hxlnt/open_spectre/documentation/analoge side.PNG

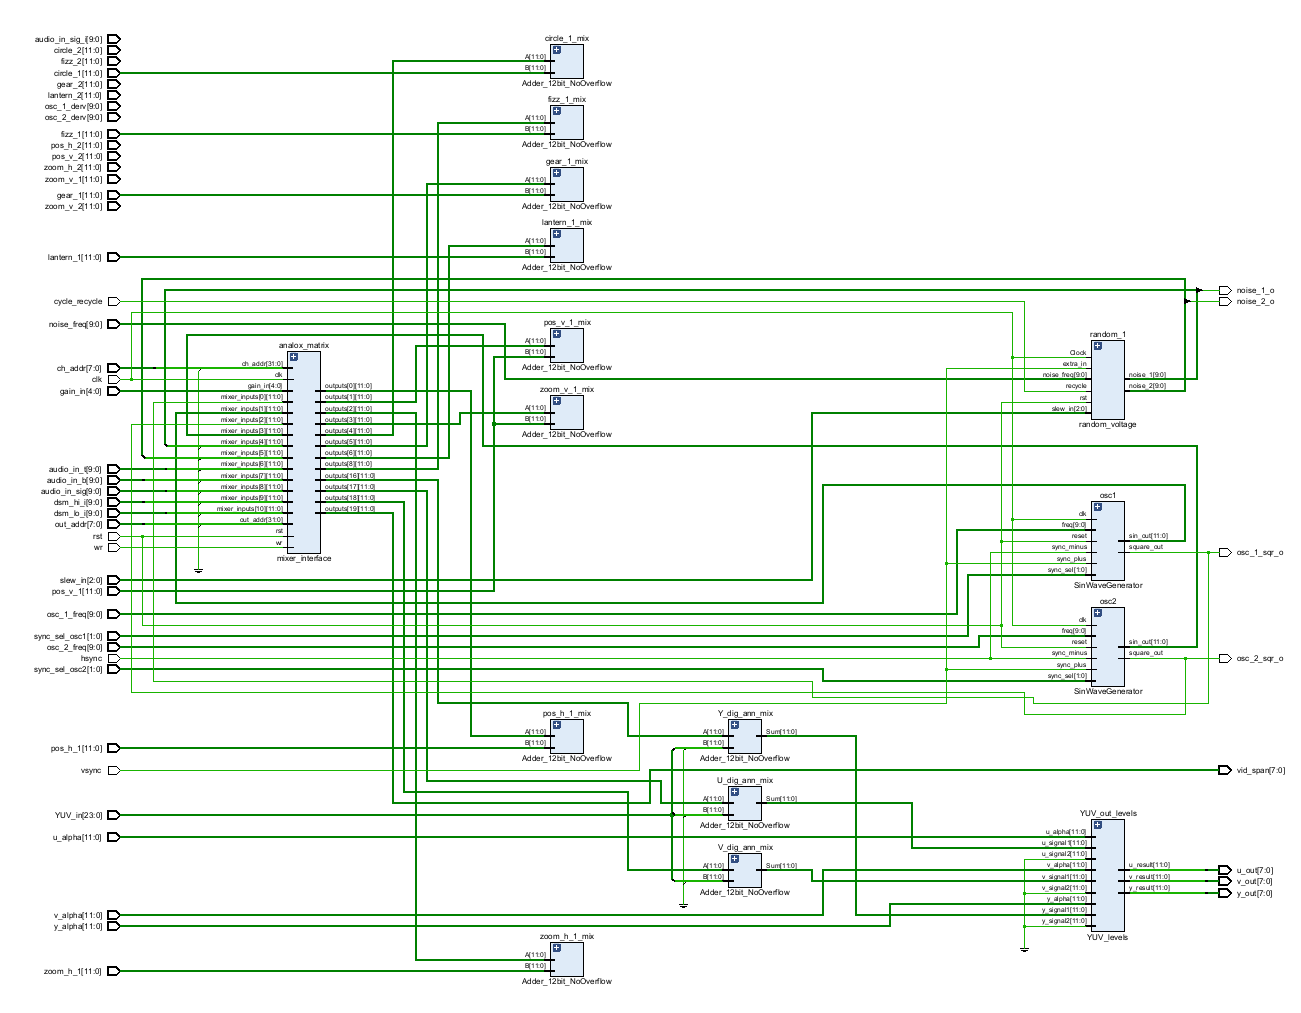
documentation/analoge side.PNG
