hxlnt/open_spectre/documentation/block design.jpg

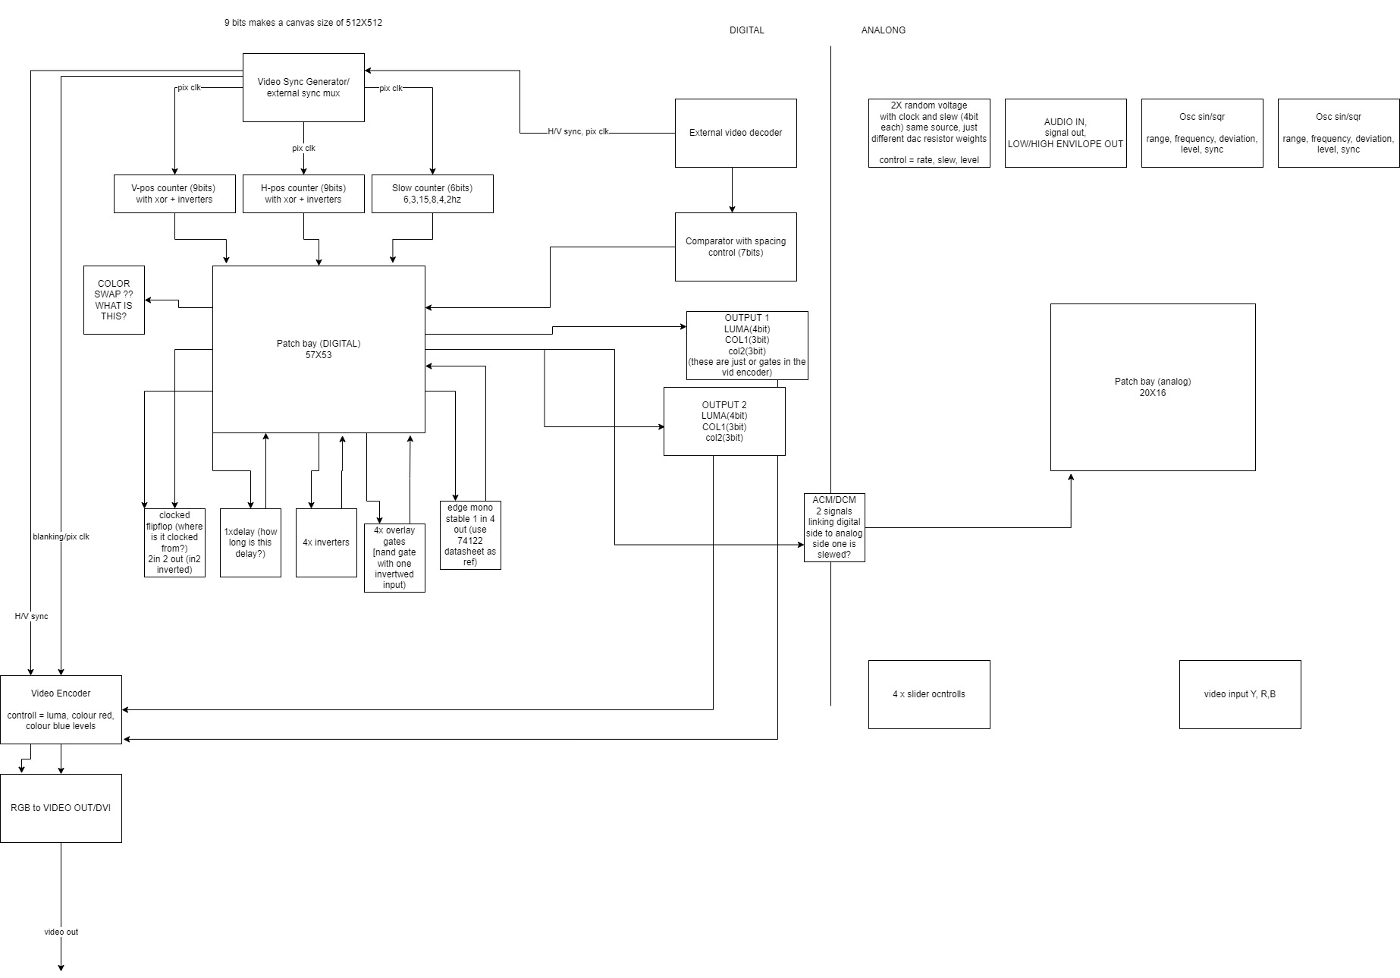
documentation/block design.jpg
