hxlnt/open_spectre/documentation/cpu_wrapper.PNG

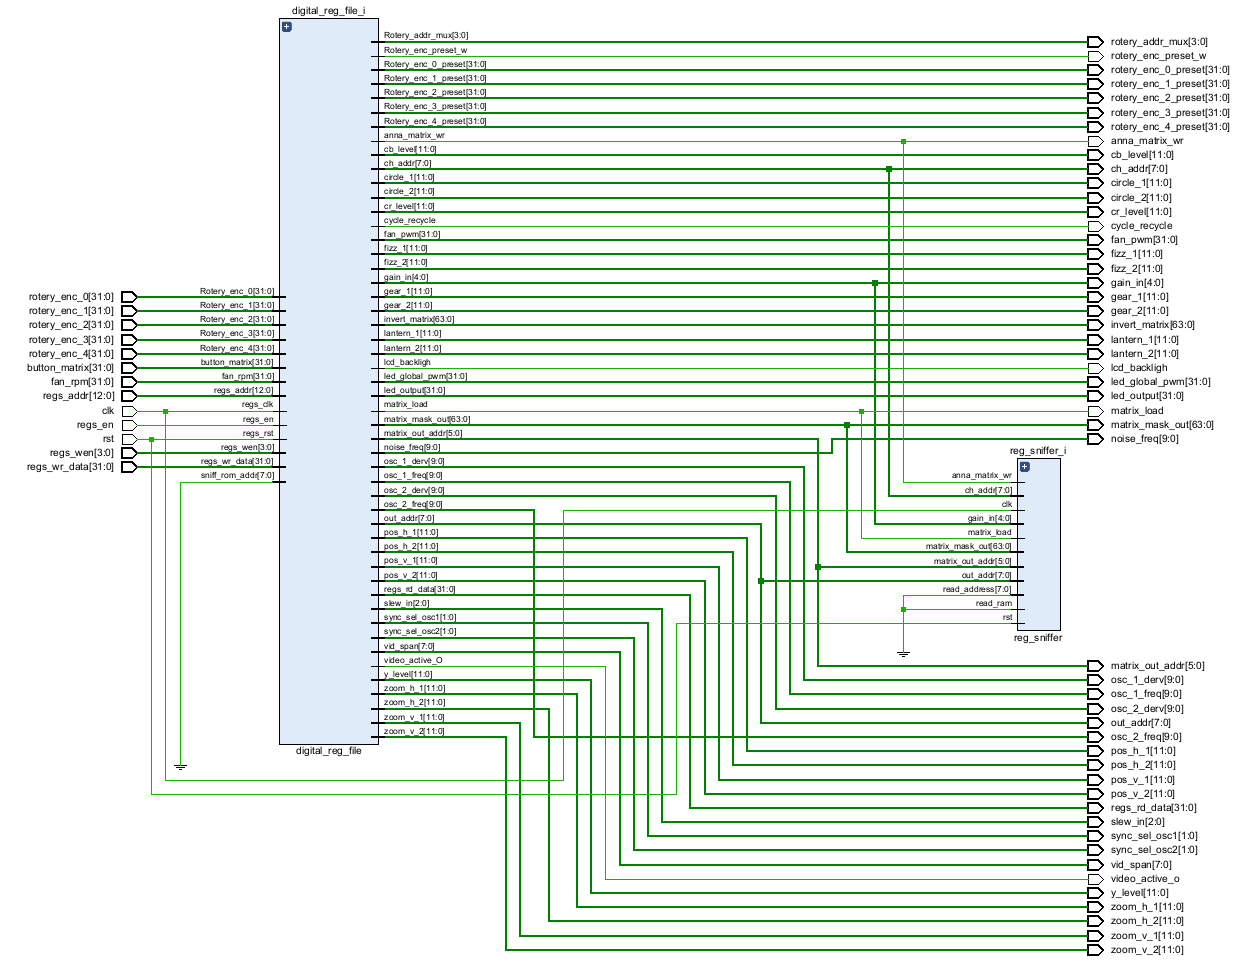
documentation/cpu_wrapper.PNG
