hxlnt/open_spectre/documentation/digital_side.PNG

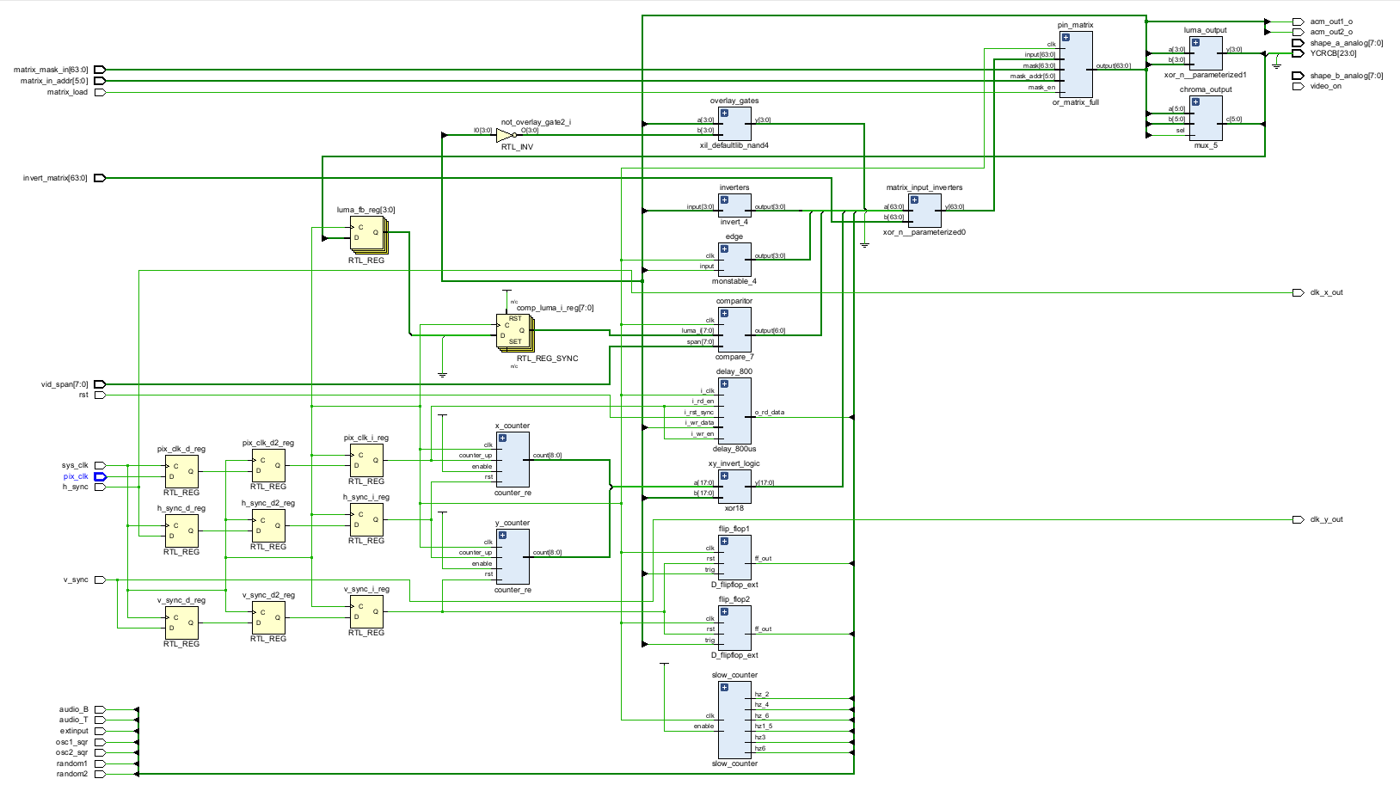
documentation/digital_side.PNG
