hxlnt/open_spectre/documentation/ems_diagram.drawio.png

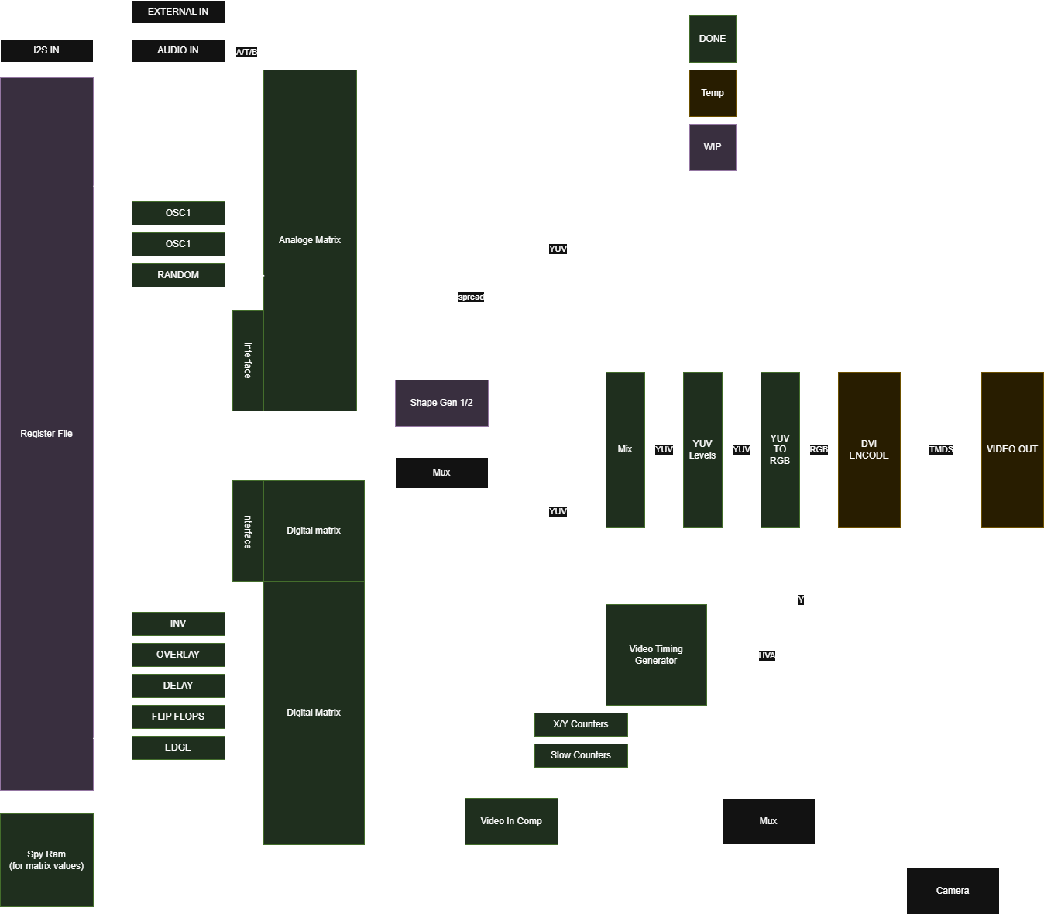
documentation/ems_diagram.drawio.png
