hxlnt/open_spectre/fpga/tools/sim_images/play1.png

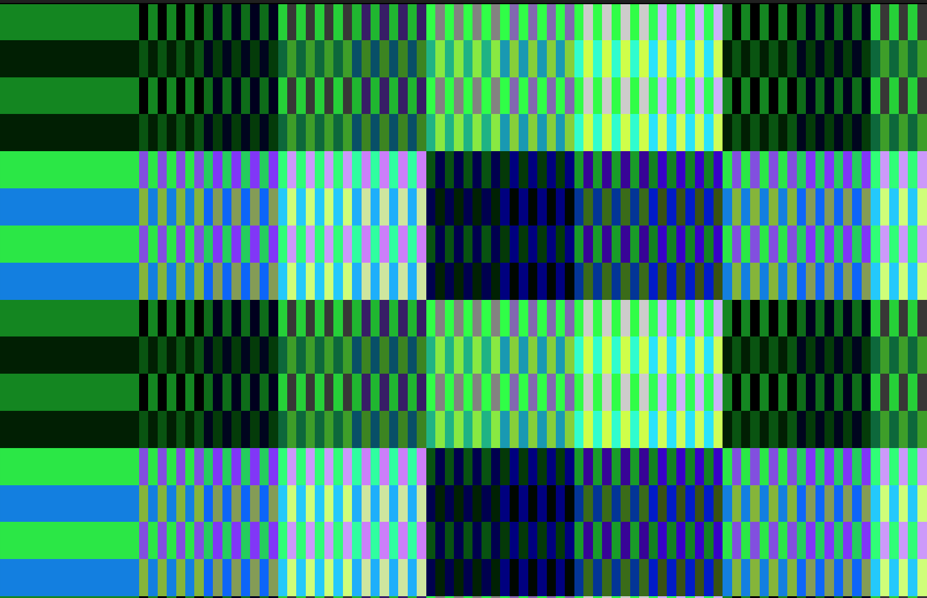
fpga/tools/sim_images/play1.png
