hxlnt/open_spectre/fpga/tools/sim_images/play2.png

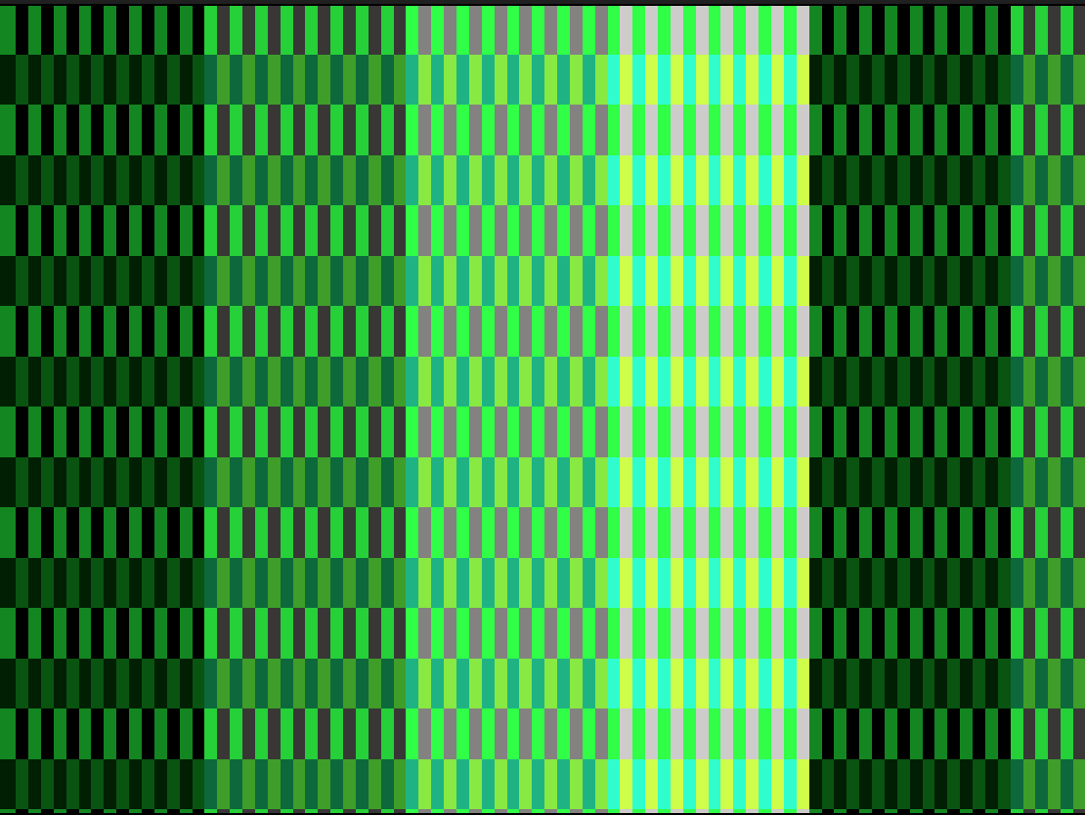
fpga/tools/sim_images/play2.png
