hxlnt/open_spectre/fpga/tools/sim_images/x&y_cnt_combo.png

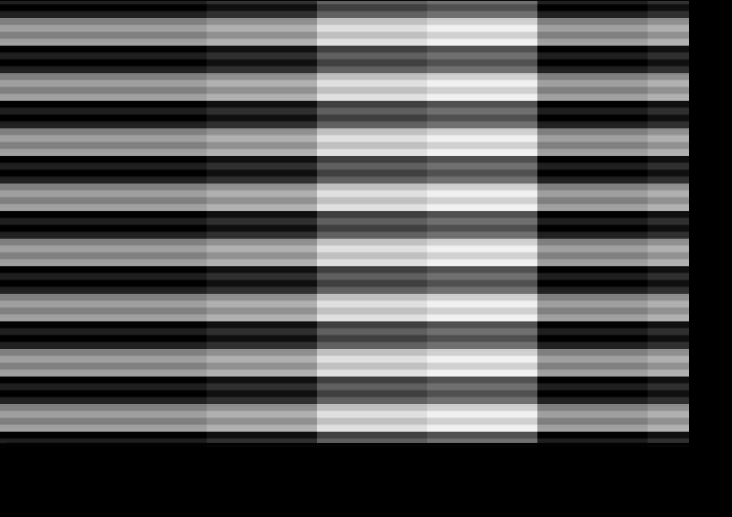
fpga/tools/sim_images/x&y_cnt_combo.png
