hxlnt/open_spectre/fpga/tools/sim_images/x_cnt_2.png

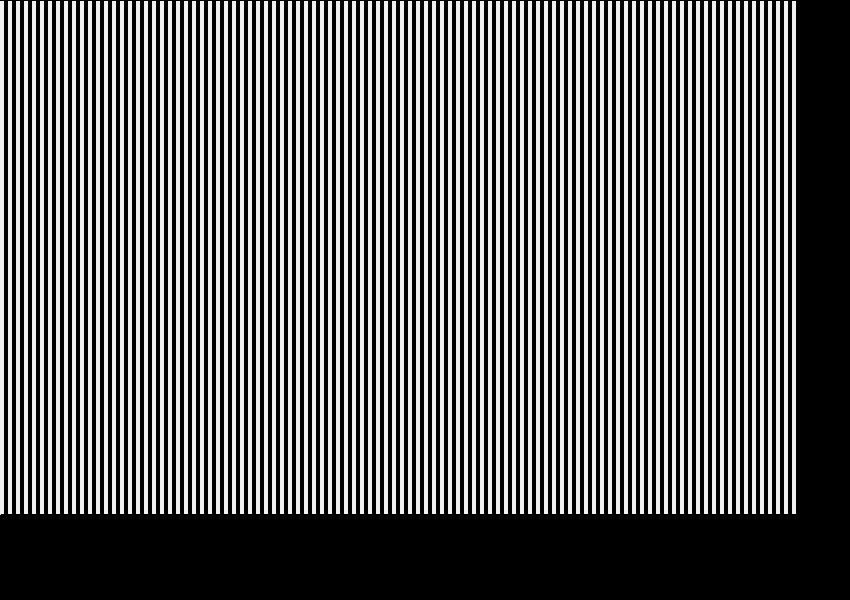
fpga/tools/sim_images/x_cnt_2.png
