hxlnt/open_spectre/fpga/tools/sim_images/x_cnt_4.png

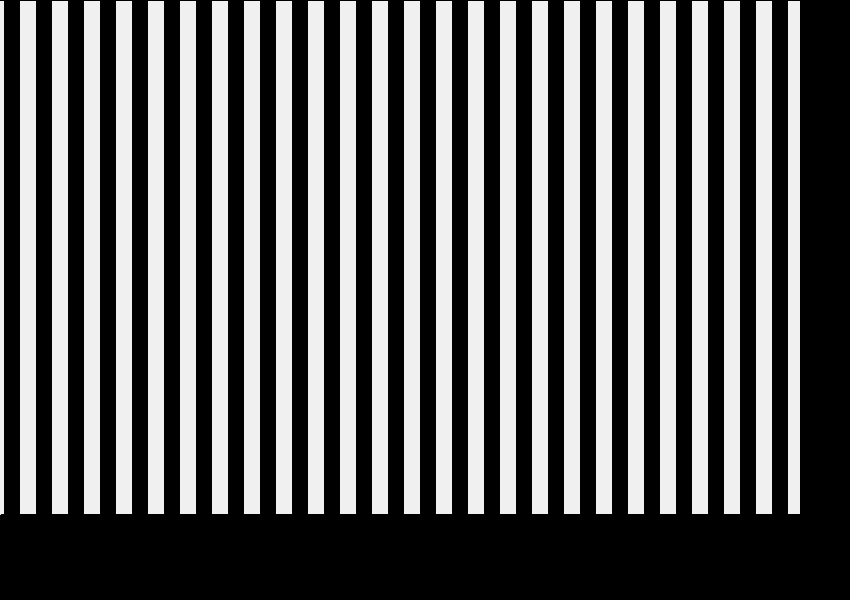
fpga/tools/sim_images/x_cnt_4.png
