hxlnt/open_spectre/fpga/tools/sim_images/x_cnt_5_blanking on now.png

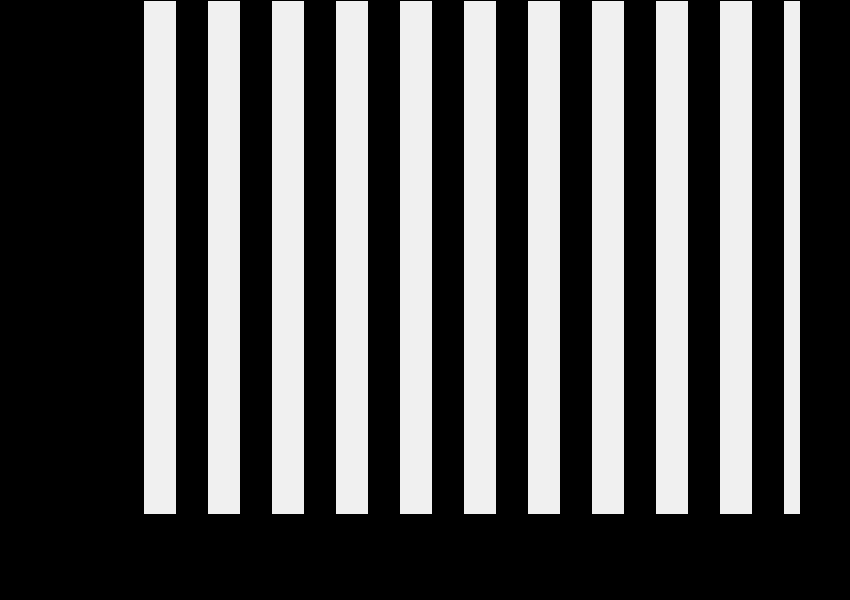
fpga/tools/sim_images/x_cnt_5_blanking on now.png
