hxlnt/open_spectre/fpga/tools/sim_images/x_cnt_6_blanking on.png

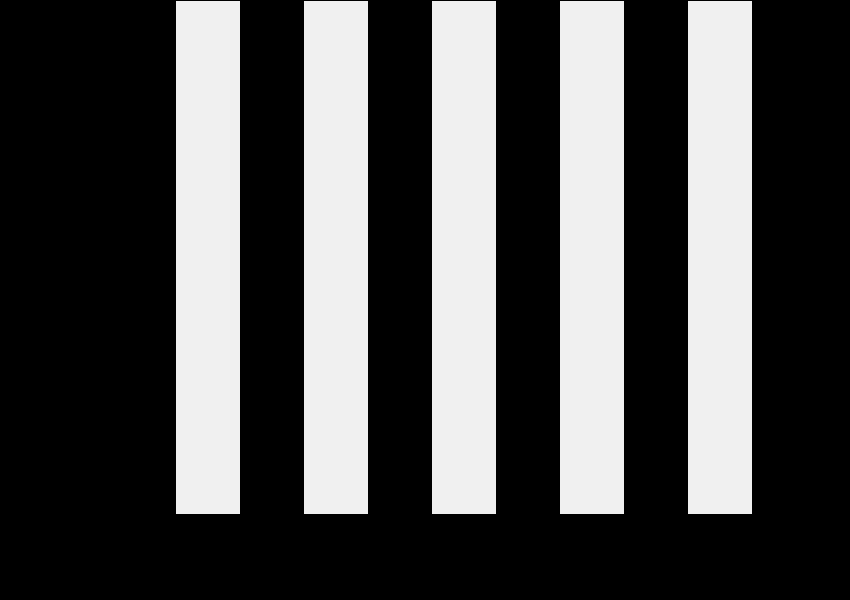
fpga/tools/sim_images/x_cnt_6_blanking on.png
