hxlnt/open_spectre/fpga/tools/sim_images/x_cnt_7 blanking on.png

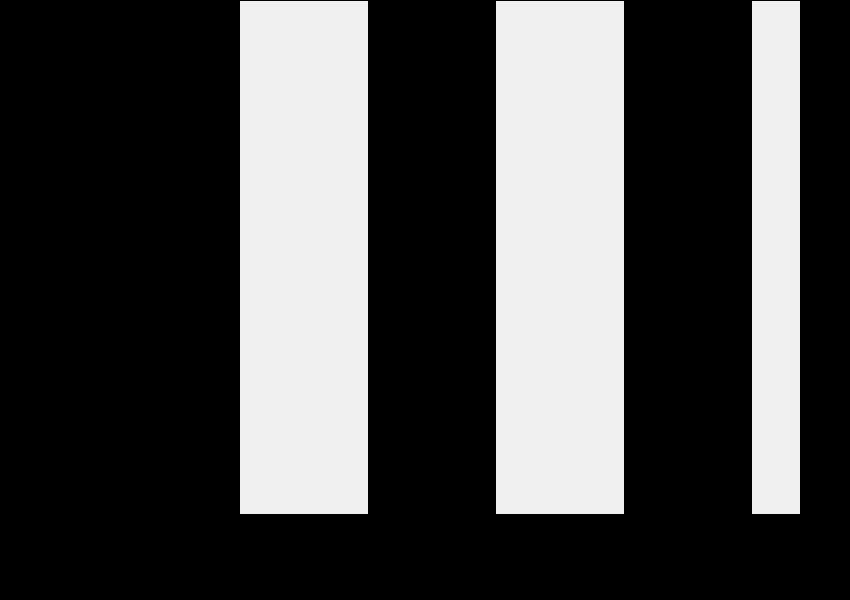
fpga/tools/sim_images/x_cnt_7 blanking on.png
