hxlnt/open_spectre/fpga/tools/sim_images/x_cnt_8 blanking on.png

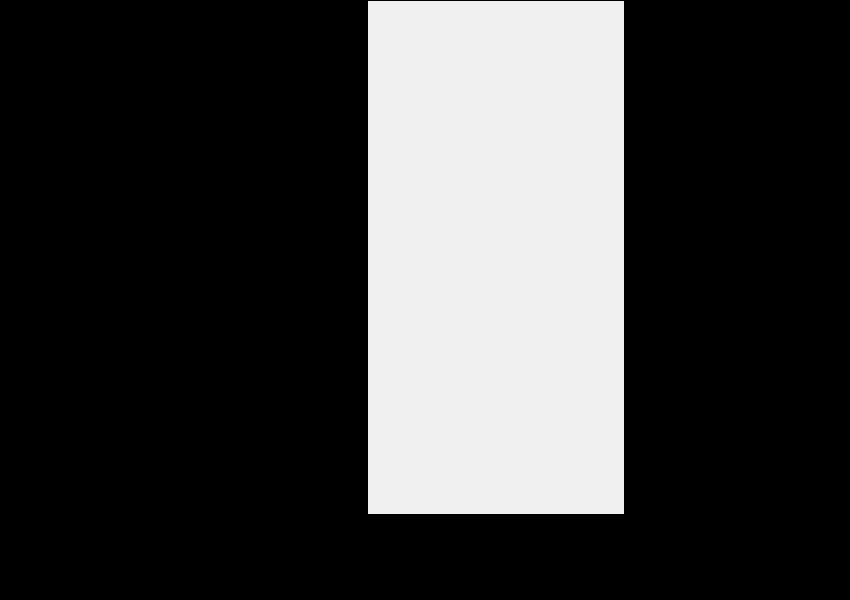
fpga/tools/sim_images/x_cnt_8 blanking on.png
