hxlnt/open_spectre/Spectron Resources/Product Photos/CBI2cJAWEAApC-f.jpg large.jpg

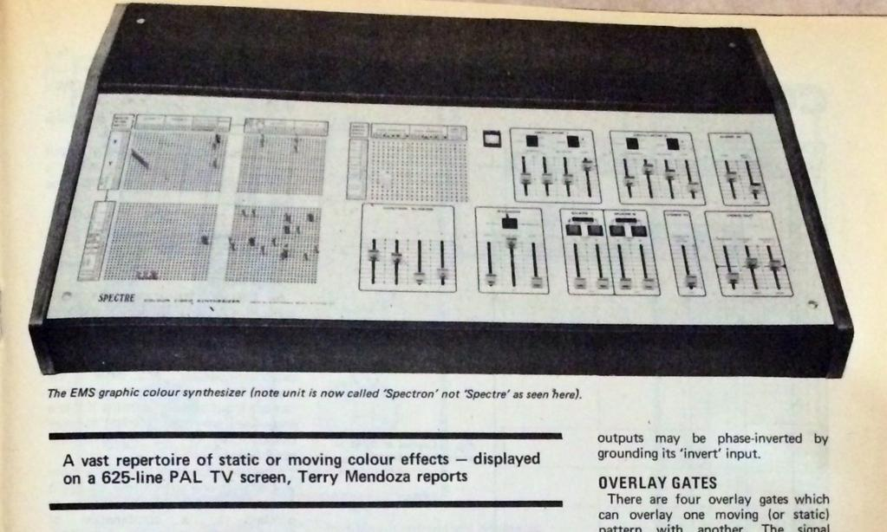
Spectron Resources/Product Photos/CBI2cJAWEAApC-f.jpg large.jpg
