hxlnt/open_spectre/Spectron Resources/Product Photos/EMS_Spectron_sheet_1_100.jpg

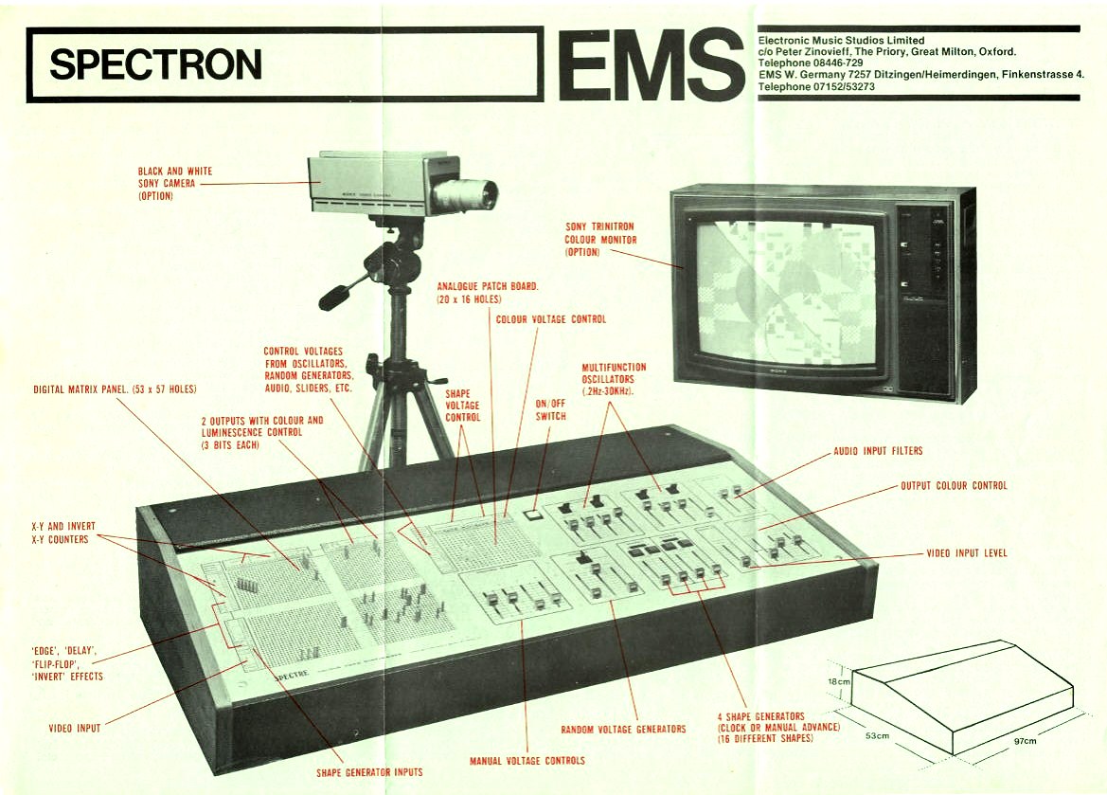
Spectron Resources/Product Photos/EMS_Spectron_sheet_1_100.jpg
