hxlnt/open_spectre/Spectron Resources/Product Photos/EMS_Spectron_sheet_2_100.jpg

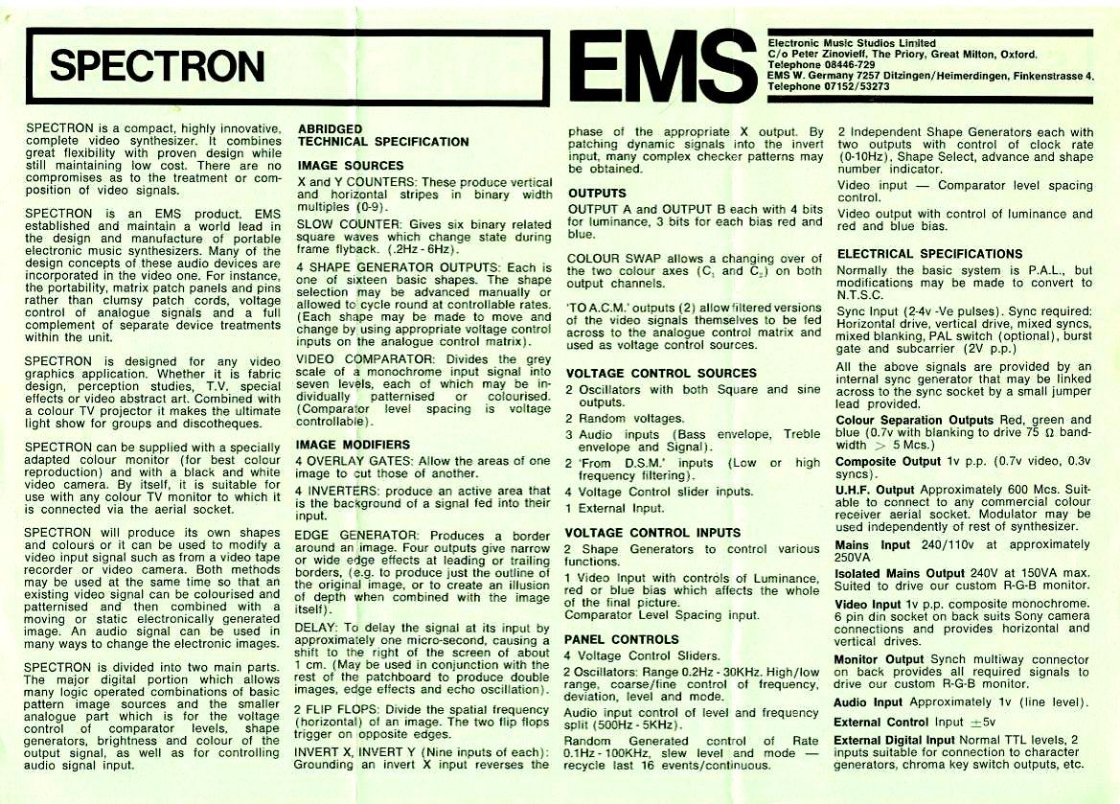
Spectron Resources/Product Photos/EMS_Spectron_sheet_2_100.jpg
