hxlnt/open_spectre/Spectron Resources/Product Photos/Flo Kaufmann_unit/IMG_1372.jpg

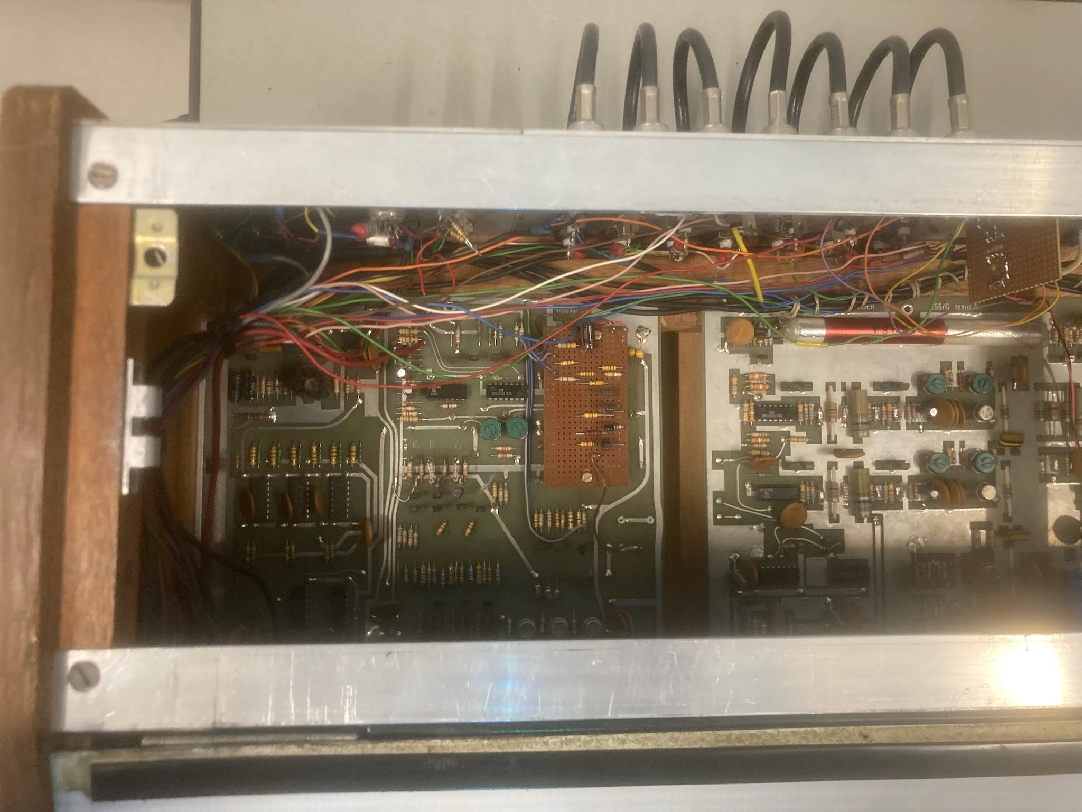
Spectron Resources/Product Photos/Flo Kaufmann_unit/IMG_1372.jpg
