hxlnt/open_spectre/Spectron Resources/Product Photos/Flo Kaufmann_unit/IMG_1391.jpg

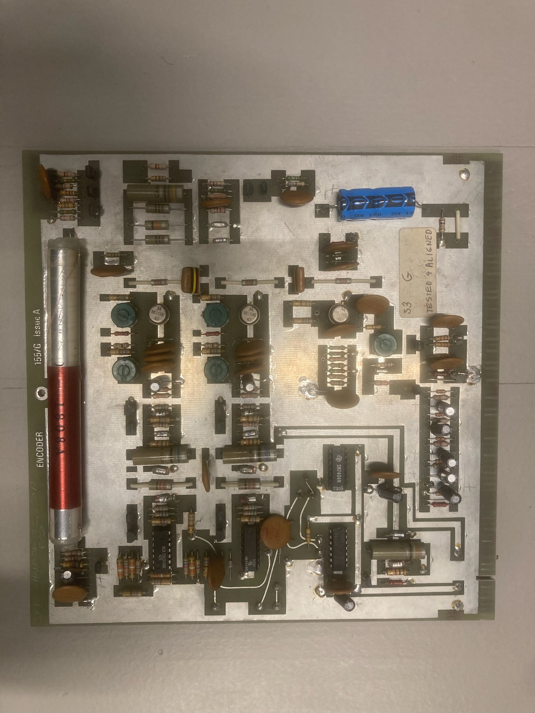
Spectron Resources/Product Photos/Flo Kaufmann_unit/IMG_1391.jpg
