hxlnt/open_spectre/Spectron Resources/Product Photos/IMG_0234.jpeg

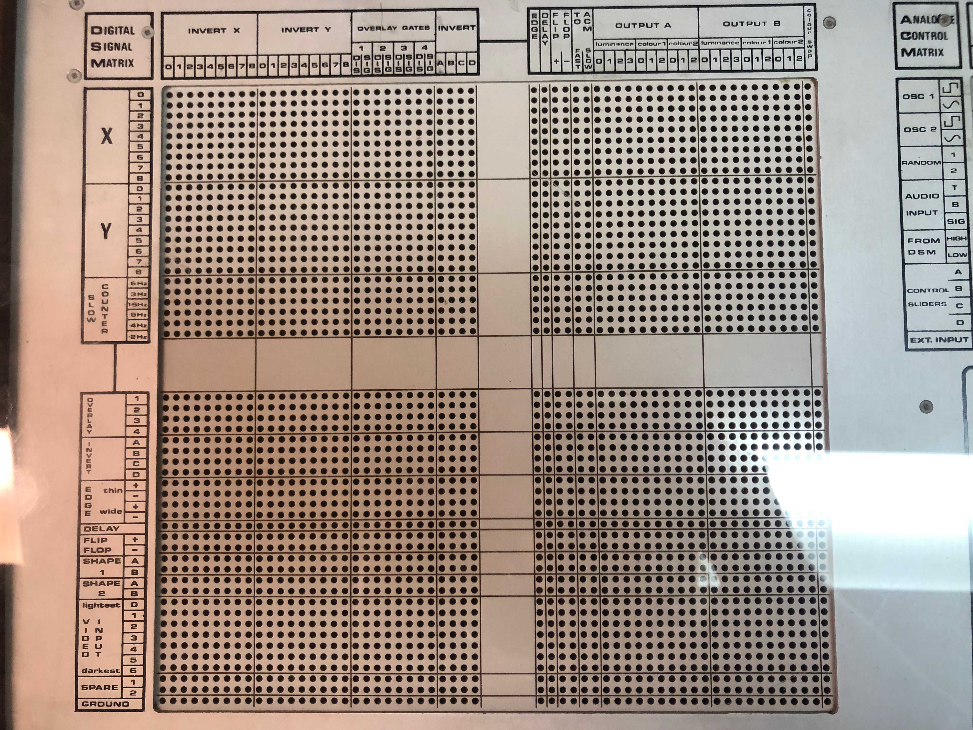
Spectron Resources/Product Photos/IMG_0234.jpeg
