hxlnt/open_spectre/Spectron Resources/Product Photos/IMG_0235.jpeg

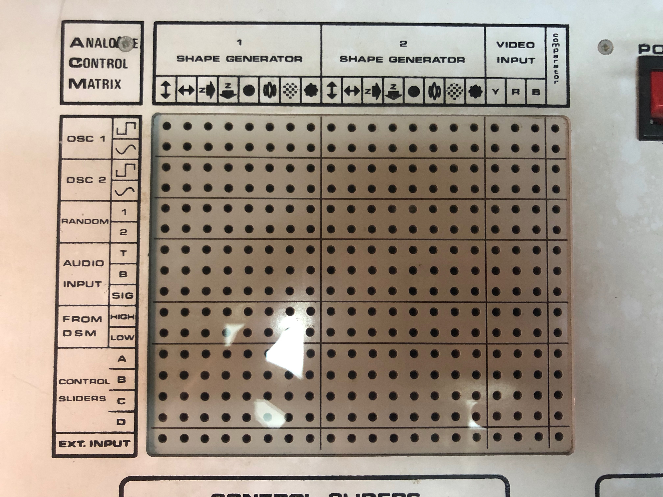
Spectron Resources/Product Photos/IMG_0235.jpeg
