hxlnt/open_spectre/Spectron Resources/Product Photos/IMG_0236.jpeg

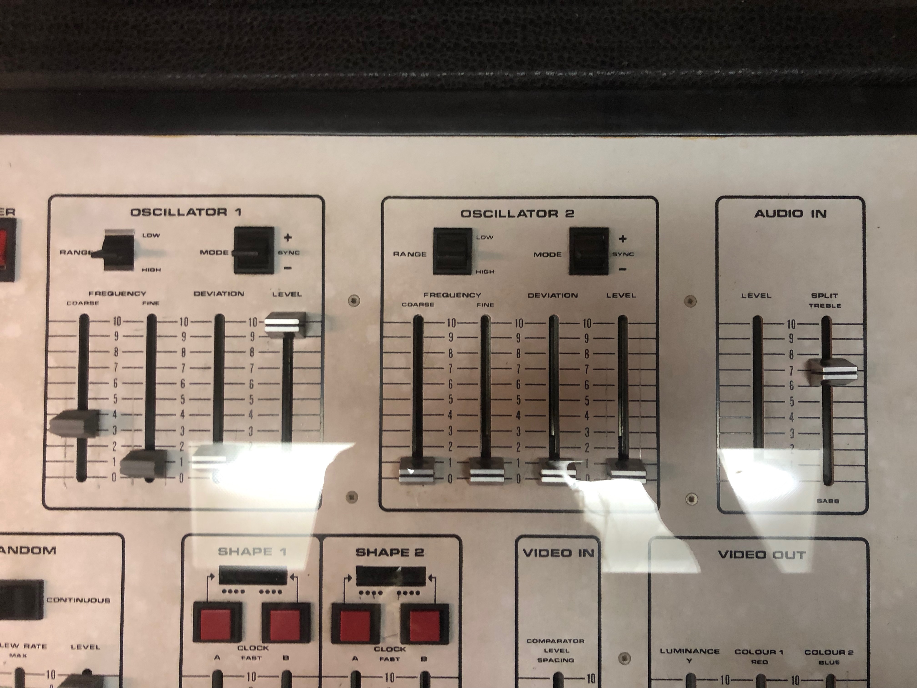
Spectron Resources/Product Photos/IMG_0236.jpeg
