hxlnt/open_spectre/Spectron Resources/Product Photos/IMG_0237.jpeg

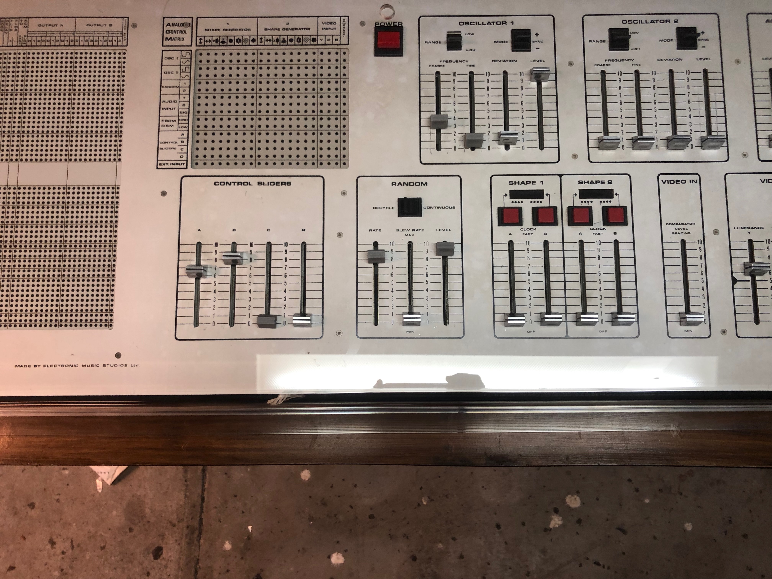
Spectron Resources/Product Photos/IMG_0237.jpeg
