hxlnt/open_spectre/Spectron Resources/Product Photos/IMG_0238.jpeg

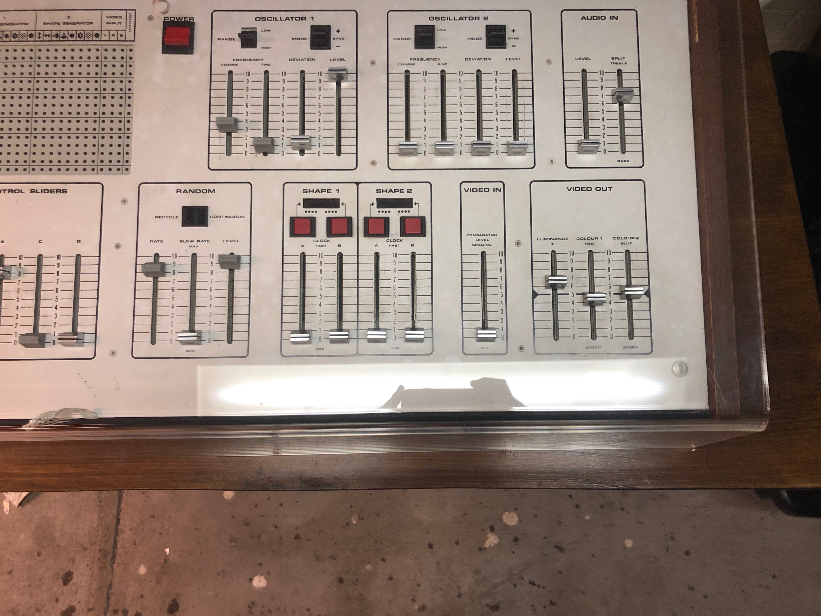
Spectron Resources/Product Photos/IMG_0238.jpeg
