hxlnt/open_spectre/Spectron Resources/Product Photos/IMG_0239.jpeg

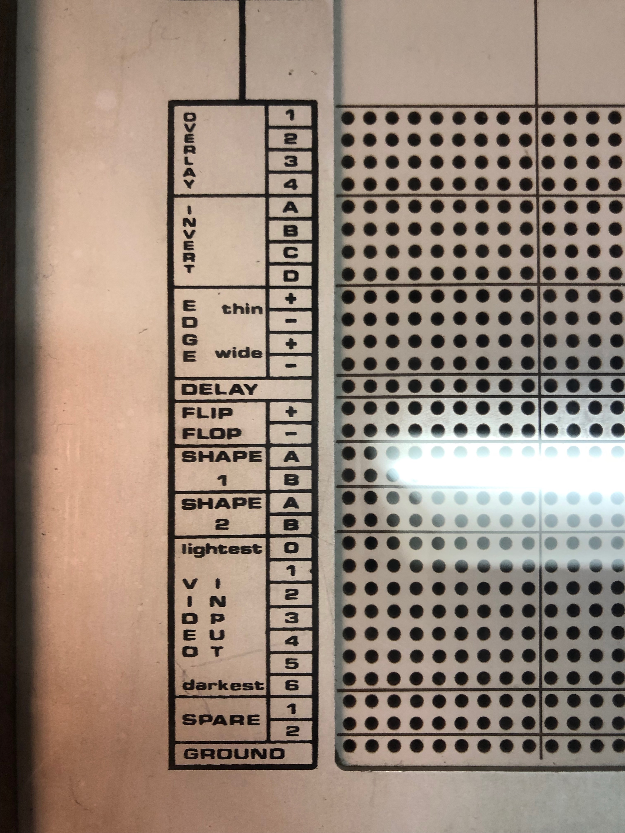
Spectron Resources/Product Photos/IMG_0239.jpeg
