hxlnt/open_spectre/Spectron Resources/Product Photos/IMG_0240.jpeg

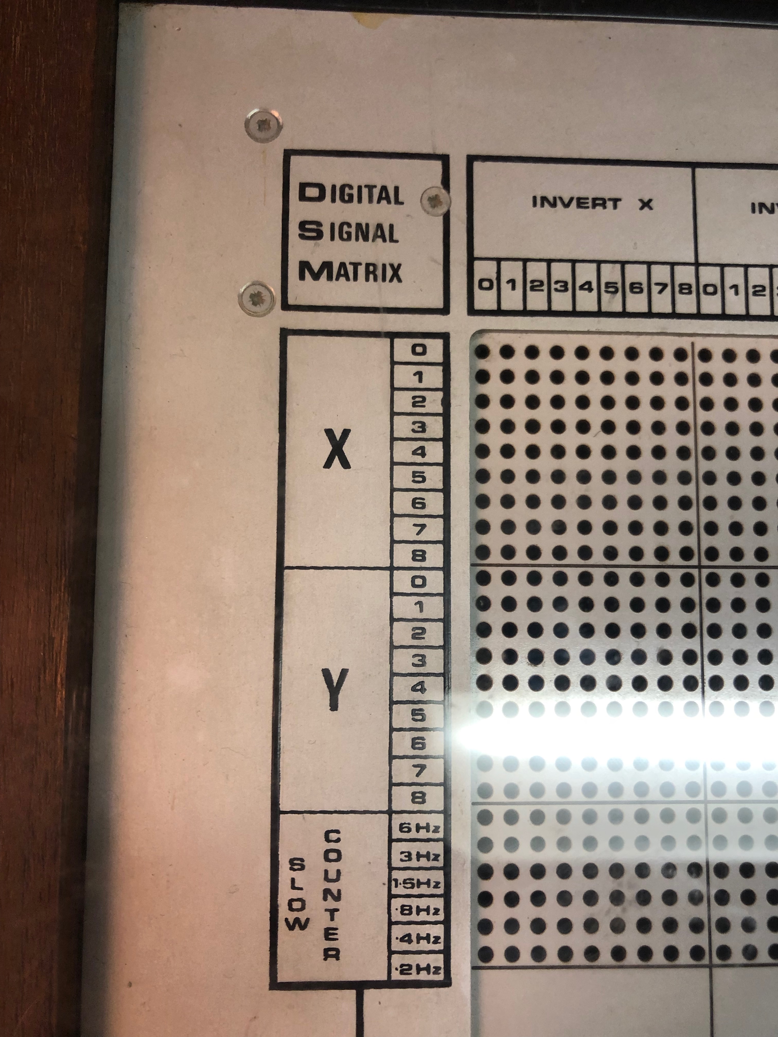
Spectron Resources/Product Photos/IMG_0240.jpeg
