hxlnt/open_spectre/Spectron Resources/Product Photos/IMG_0241.jpeg

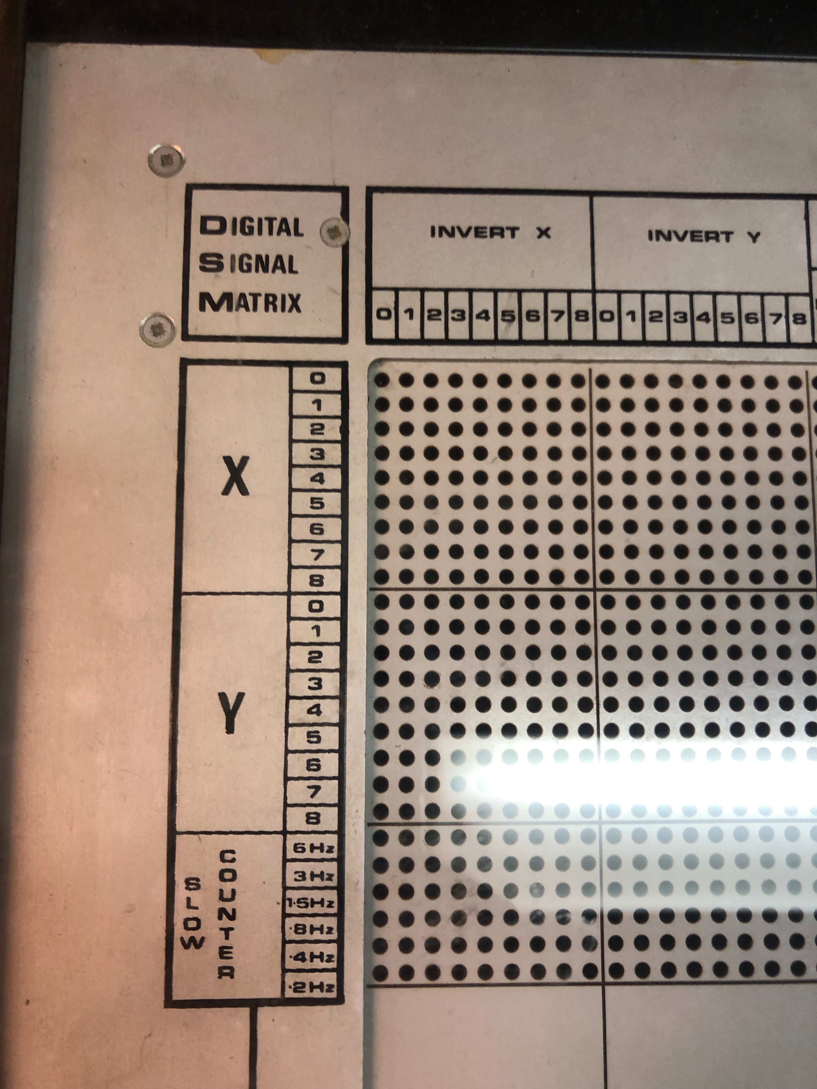
Spectron Resources/Product Photos/IMG_0241.jpeg
