hxlnt/open_spectre/Spectron Resources/Product Photos/IMG_0242.jpeg

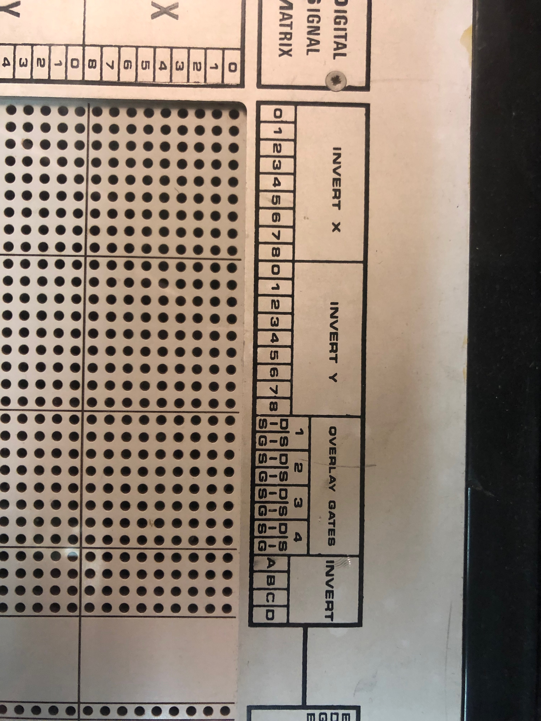
Spectron Resources/Product Photos/IMG_0242.jpeg
