hxlnt/open_spectre/Spectron Resources/Product Photos/IMG_0243.jpeg

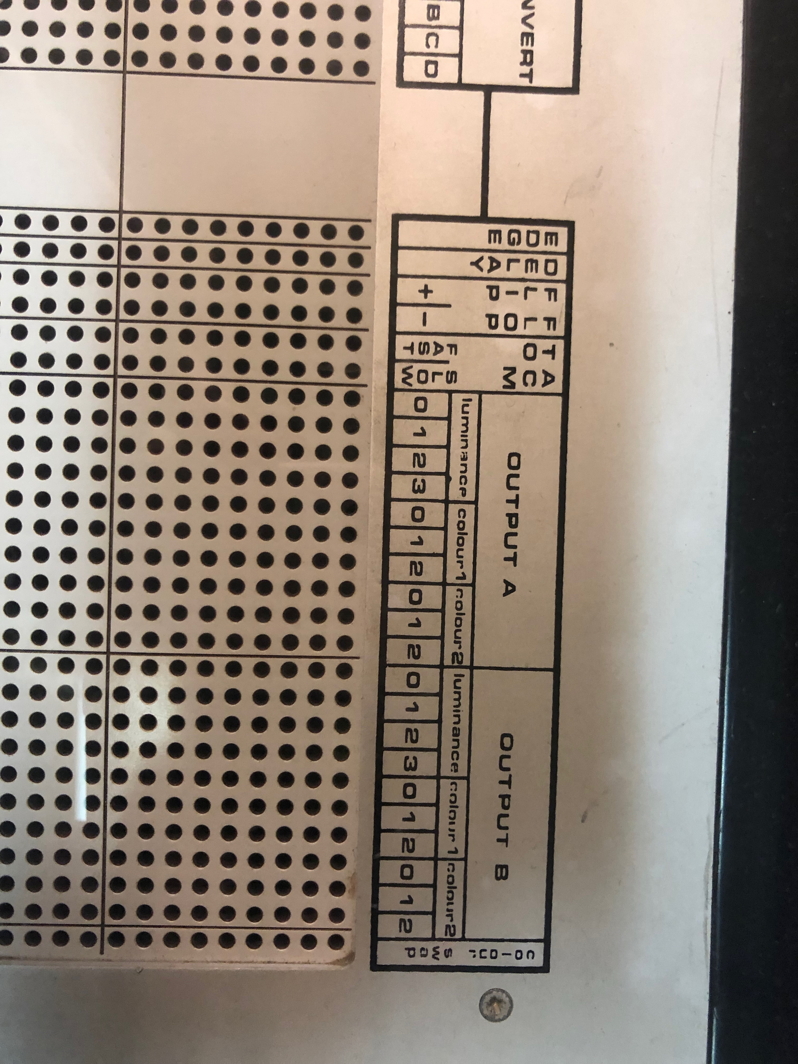
Spectron Resources/Product Photos/IMG_0243.jpeg
