hxlnt/open_spectre/Spectron Resources/Product Photos/IMG_0245.jpeg

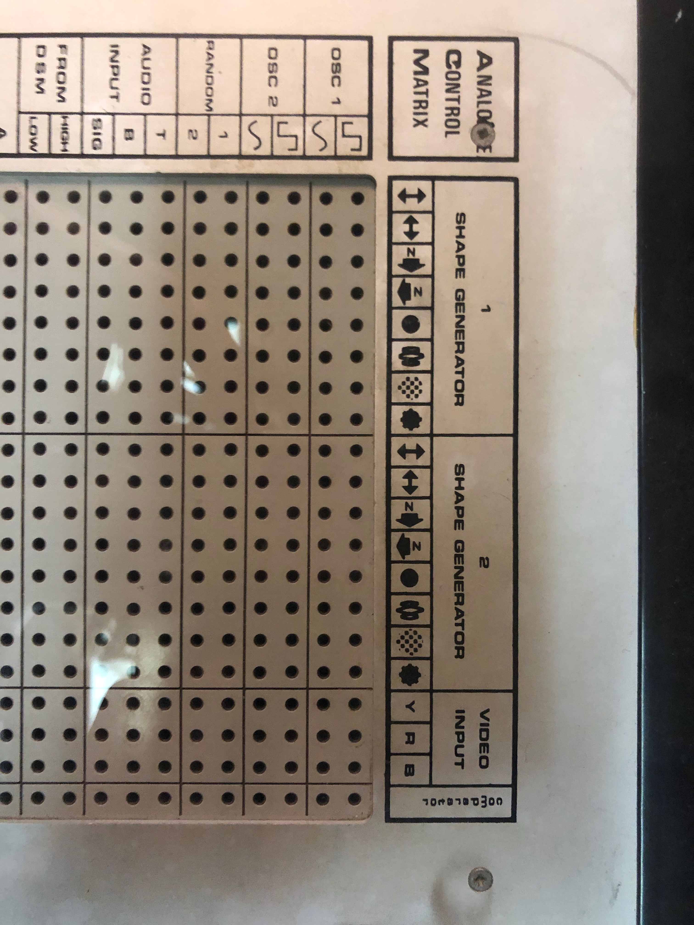
Spectron Resources/Product Photos/IMG_0245.jpeg
