hxlnt/open_spectre/Spectron Resources/Product Photos/IMG_0246.jpeg

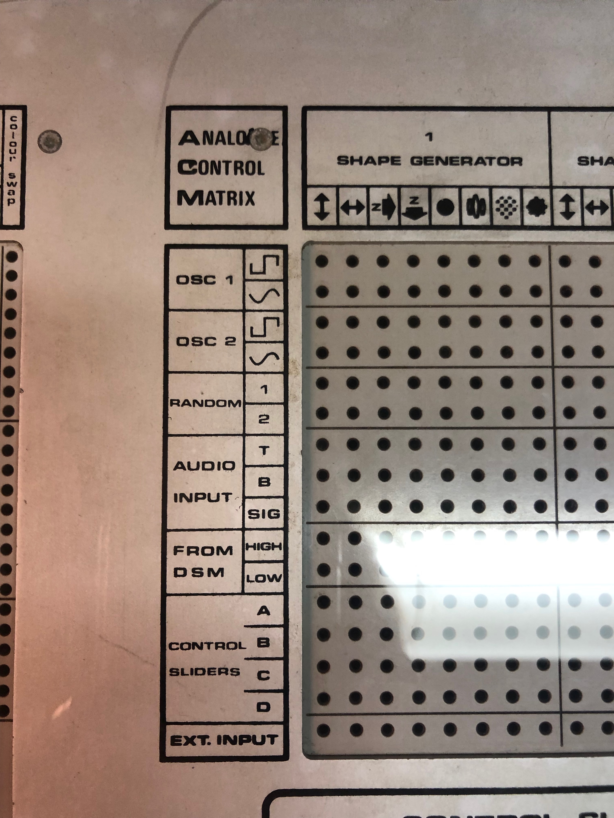
Spectron Resources/Product Photos/IMG_0246.jpeg
