hxlnt/open_spectre/Spectron Resources/Product Photos/Other machines/videosiz1.jpg

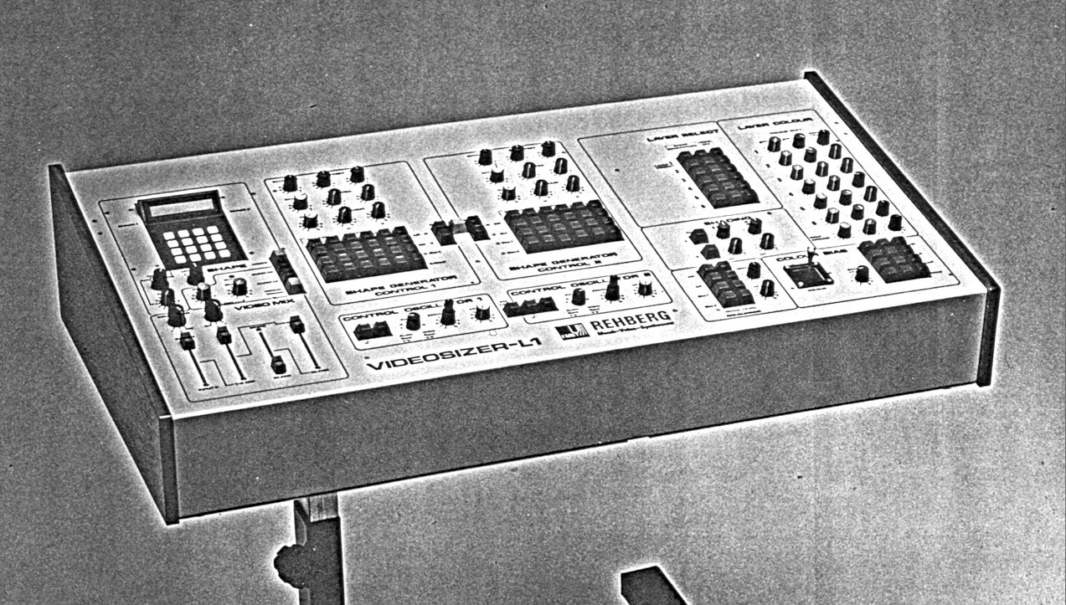
Spectron Resources/Product Photos/Other machines/videosiz1.jpg
