hxlnt/open_spectre/Spectron Resources/Product Photos/Other machines/videosiz1x.jpg

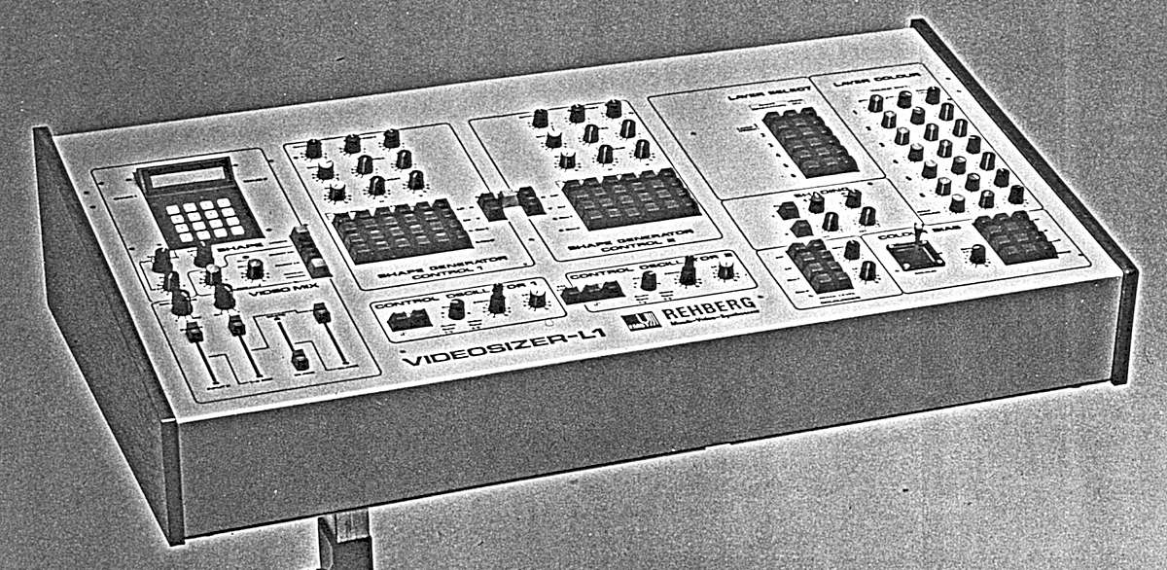
Spectron Resources/Product Photos/Other machines/videosiz1x.jpg
