hxlnt/open_spectre/Spectron Resources/Product Photos/Other machines/videosiz2.jpg

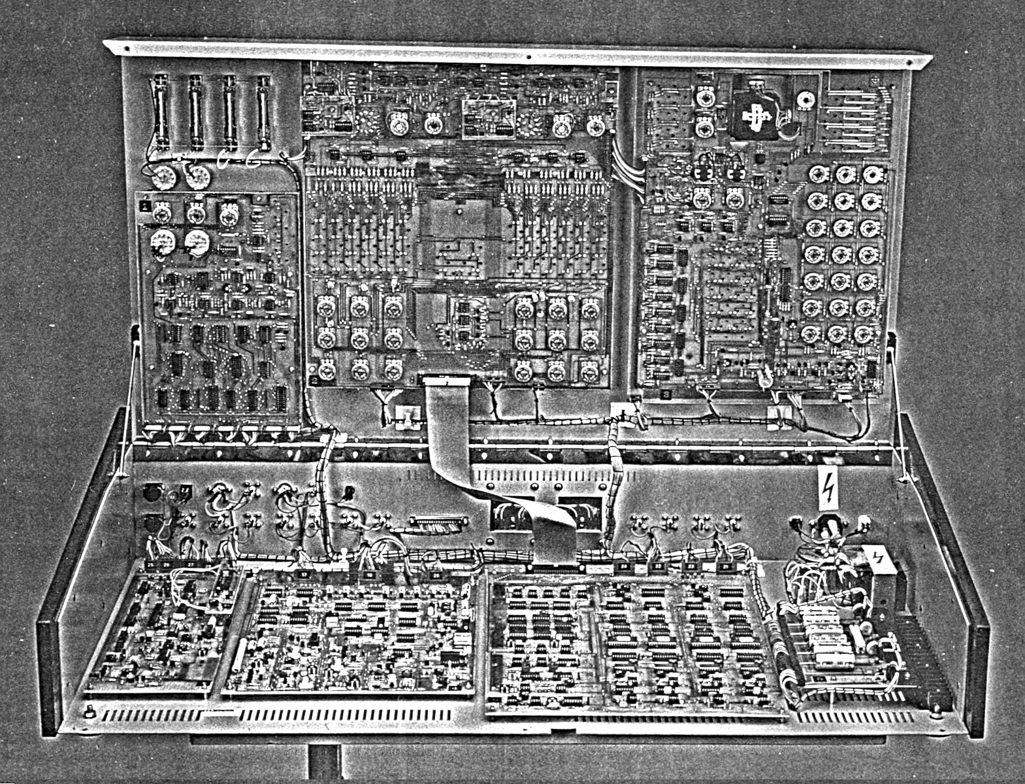
Spectron Resources/Product Photos/Other machines/videosiz2.jpg
