hxlnt/open_spectre/Spectron Resources/Product Photos/Richard Smiths Spectron.jpg

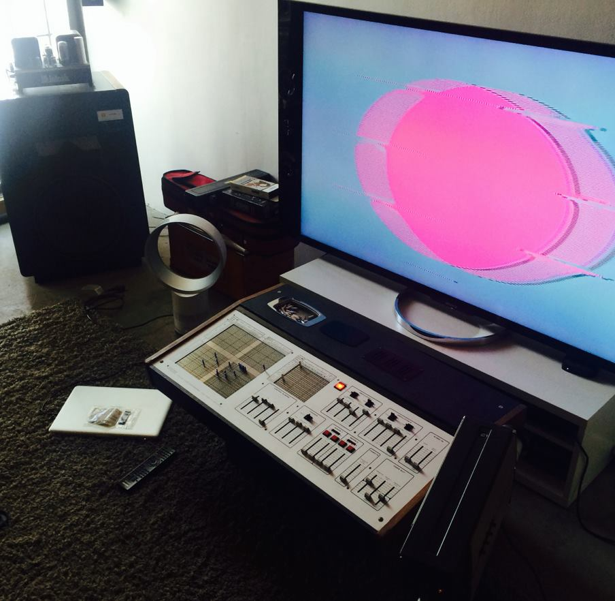
Spectron Resources/Product Photos/Richard Smiths Spectron.jpg
