hxlnt/open_spectre/Spectron Resources/Product Photos/spectre1x (1).jpg

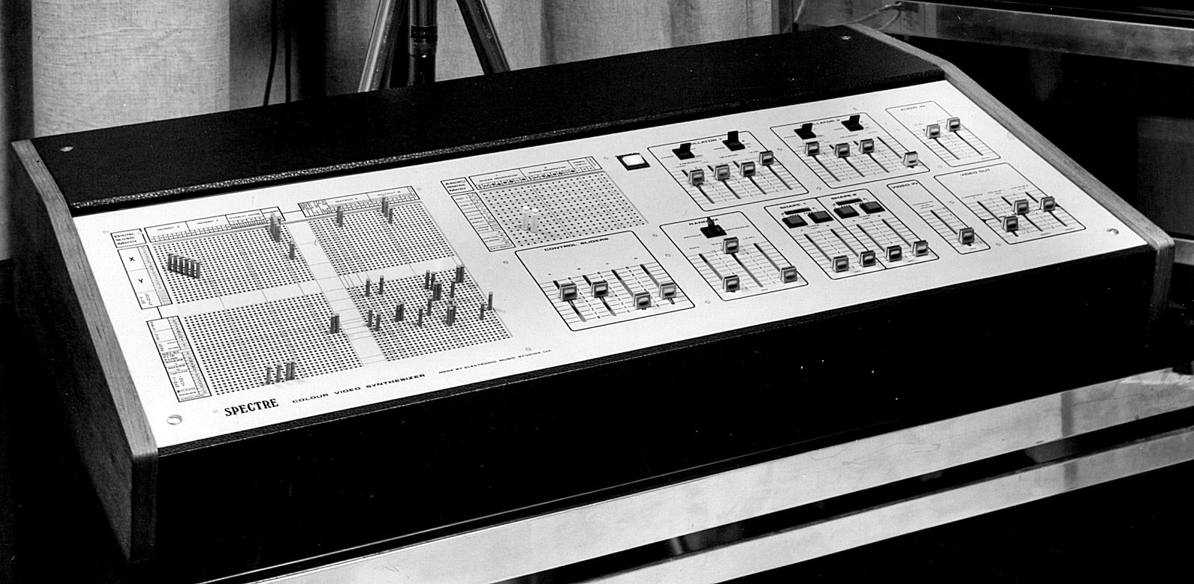
Spectron Resources/Product Photos/spectre1x (1).jpg
