hxlnt/open_spectre/documentation/devlog/playlist.png

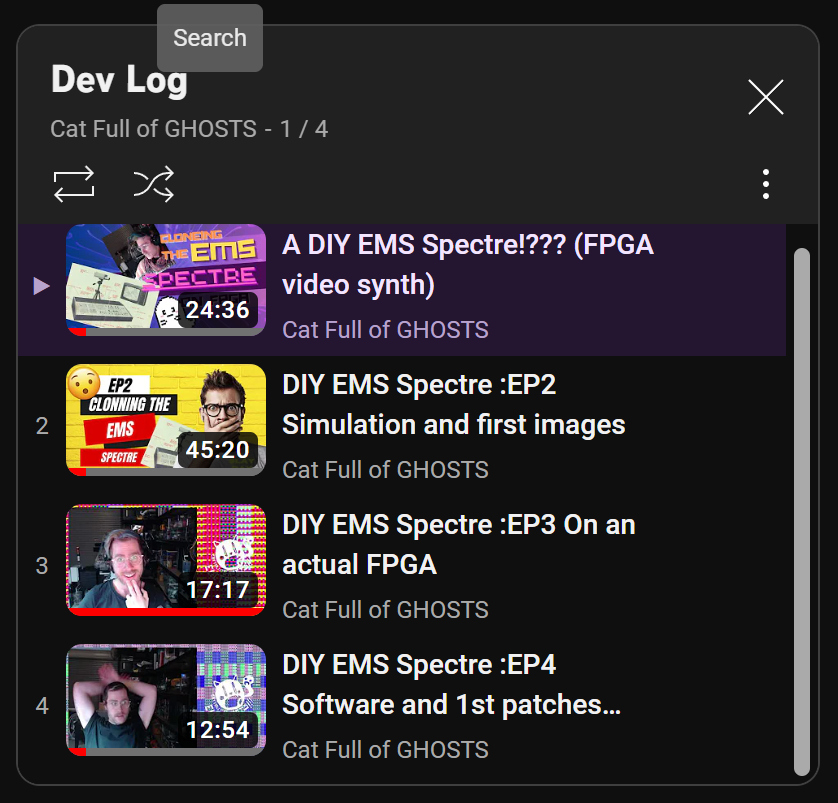
documentation/devlog/playlist.png
