hxlnt/open_spectre/fpga/src/analoge_side/osc/SinWaveGenerator.vhdl

--   ____  _____  ______ _   _         _____ _____  ______ _____ _______ _____  ______ 
--  / __ \|  __ \|  ____| \ | |       / ____|  __ \|  ____/ ____|__   __|  __ \|  ____|
-- | |  | | |__) | |__  |  \| |      | (___ | |__) | |__ | |       | |  | |__) | |__   
-- | |  | |  ___/|  __| | . ` |       \___ \|  ___/|  __|| |       | |  |  _  /|  __|  
-- | |__| | |    | |____| |\  |       ____) | |    | |___| |____   | |  | | \ \| |____ 
--  \____/|_|    |______|_| \_|      |_____/|_|    |______\_____|  |_|  |_|  \_\______|
--                               ______                                                
--                              |______|      
-- Create Date: 2023
-- Created by: Rob D Jordan
-- Notes: Sinewave ROM should live somewhere cleaner.

library IEEE;
use IEEE.STD_LOGIC_1164.ALL;
use IEEE.numeric_std.ALL;
use IEEE.STD_LOGIC_UNSIGNED.ALL;

entity SinWaveGenerator is
    Port (
        clk : in STD_LOGIC;
        reset : in STD_LOGIC;
        freq : in STD_LOGIC_VECTOR(9 downto 0);
        sync_sel : in STD_LOGIC_VECTOR(1 downto 0);
        sync_plus : in STD_LOGIC;
        sync_minus : in STD_LOGIC;
        dist_level      : in STD_LOGIC_VECTOR(7 downto 0) := (others => '0'); -- distortion wave level
        sin_out : out STD_LOGIC_VECTOR(11 downto 0);
        square_out : out STD_LOGIC
    );
end SinWaveGenerator;

architecture Behavioral of SinWaveGenerator is
    signal counter, counterB : STD_LOGIC_VECTOR(13 downto 0) := (others => '0');
    signal scaled_freq : STD_LOGIC_VECTOR(13 downto 0) := (others => '0');

    signal phase_accumulator,phase_accumulatorB:  integer range 0 to 180;--unsigned(13 downto 0) := (others => '0');  -- Use 12 bits for phase accumulator
    signal rom_address, rom_address_dist : integer range 0 to 180;
    signal sine_table, sine_table_dist,sin_table_xmod : STD_LOGIC_VECTOR(11 downto 0);
    signal sine_table_summed, sine_table_summed_limited : STD_LOGIC_VECTOR(12 downto 0);
    signal square_i : STD_LOGIC := '0';
    signal sync_edge : STD_LOGIC := '0';
    signal sync_in : STD_LOGIC := '0';
    signal dist_freq : STD_LOGIC_VECTOR(13 downto 0) := (others => '1');
    
      signal atten_val    : unsigned(11 downto 0);
  signal atten_val_d    : unsigned(11 downto 0);
    
    --
    
    signal attenuated_out   : STD_LOGIC_VECTOR(11 downto 0);

    type ROM is array (0 to 360) of STD_LOGIC_VECTOR(11 downto 0); -- i think this only needs to be 180
    constant sine_rom : ROM := (
"011111111111",
"100001000110",
"100010001101",
"100011010100",
"100100011011",
"100101100010",
"100110101000",
"100111101110",
"101000110011",
"101001110111",
"101010111011",
"101011111101",
"101100111111",
"101110000000",
"101111000000",
"101111111110",
"110000111011",
"110001110111",
"110010110010",
"110011101011",
"110100100010",
"110101011000",
"110110001100",
"110110111111",
"110111110000",
"111000011111",
"111001001100",
"111001110111",
"111010100000",
"111011000110",
"111011101011",
"111100001110",
"111100101110",
"111101001101",
"111101101000",
"111110000010",
"111110011001",
"111110101110",
"111111000001",
"111111010001",
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
    );

begin

    scaled_freq <= freq & "0000";
    dist_freq <= "00" & freq & "11";

    process(clk, reset, sync_in)
    begin
        if reset = '1' then
            counter <= (others => '0');
            counterB <= (others => '0');
            phase_accumulator <= 0;
            phase_accumulatorB <= 0;
            sync_edge <= '0';
        elsif rising_edge(clk) then
        
            if sync_sel = "00" then
                sync_in <= '0';
            elsif sync_sel = "01" then
                sync_in <= sync_plus;
            elsif sync_sel = "10" then 
                sync_in <= sync_minus;
            end if;
        
            if sync_in = '1' and sync_edge = '0' then
                sync_edge <= '1';
                counter <= (others => '0');
                phase_accumulator <= 0;
            else
                sync_edge <= sync_in;
                counter <= counter + 1;
                counterB <= counterB + 1;
                if rom_address > 90 then
                    square_i <= '1';
                    else 
                    square_i <= '0';
                    end if; 
                if counter = scaled_freq then
                    counter <= (others => '0');
                    phase_accumulator <= phase_accumulator + 1;
--                    if phase_accumulator = "11111111111111" then  -- Adjust the limit for 12 bits
--                        phase_accumulator <= (others => '0');
--                    end if;                    
                end if;
                if counterB = dist_freq then
                    counterB <= (others => '0');
                    phase_accumulatorB <= phase_accumulatorB + 1;
--                    if phase_accumulatorB = "11111111111111" then  -- Adjust the limit for 12 bits
--                        phase_accumulatorB <= (others => '0');
--                    end if;                    
                end if;
                
            end if;
        end if;
    end process;


   
    
process(clk) -- ff the output to lower the logic levels in the acumulator path
begin
  if rising_edge(clk) then
      -- ROM lookup
    rom_address <= phase_accumulator;-- to_integer(unsigned(phase_accumulator)) mod 180 ; -- how manny entries are ther in my sin table?? 180 or 360
    -- Distort wave lookup
    rom_address_dist <= phase_accumulatorB;-- to_integer(unsigned(phase_accumulatorB)) mod 180 ;
    -- Create the full sine wave using symmetry
    sine_table <= sine_rom(rom_address);
    -- Create the distortion sinwave
    sine_table_dist <= sine_rom(rom_address_dist); -- needs to have a amplitude control to mix the level
    end if;
    end process;
    
process(clk) -- modulate the sinwave by the attenuated other sinwave
  variable mult_resultA : unsigned(19 downto 0); -- 12+8
  variable mult_resultB : unsigned(23 downto 0); -- 12+8
--  variable atten_val    : unsigned(11 downto 0);
--  variable atten_val_d    : unsigned(11 downto 0);

begin
  if rising_edge(clk) then
    -- Step 1: attenuate distortion
    mult_resultA := unsigned(sine_table_dist) * (unsigned(dist_level));  -- 12 x 8
    atten_val <= mult_resultA(19 downto 8);  -- keep 12 bits

    -- Save result
--    attenuated_out <= std_logic_vector(atten_val);
    atten_val_d <= atten_val; 

    -- Step 2: use it to attenuate main sine
    mult_resultB := unsigned(sine_table) * (4095 - atten_val_d);
    sin_table_xmod <= std_logic_vector(mult_resultB(23 downto 12));
  end if;
end process;
    
--    process(clk) 
--        begin
--        if rising_edge(clk) then
--        sine_table_summed <= ('0'& sine_table) + ('0' & attenuated_out); 

--        if sine_table_summed(12) = '1' then
--            sine_table_summed_limited <= (others => '1');
--         else
--            sine_table_summed_limited <= sine_table_summed;
--         end if;
         
--          end if;
        
--        end process;

    sin_out <= sin_table_xmod;
    square_out <= square_i;

end Behavioral;
