hxlnt/open_spectre/fpga/src/analoge_side/annaloge_output/YUV_levels.vhd

--   ____  _____  ______ _   _         _____ _____  ______ _____ _______ _____  ______ 
--  / __ \|  __ \|  ____| \ | |       / ____|  __ \|  ____/ ____|__   __|  __ \|  ____|
-- | |  | | |__) | |__  |  \| |      | (___ | |__) | |__ | |       | |  | |__) | |__   
-- | |  | |  ___/|  __| | . ` |       \___ \|  ___/|  __|| |       | |  |  _  /|  __|  
-- | |__| | |    | |____| |\  |       ____) | |    | |___| |____   | |  | | \ \| |____ 
--  \____/|_|    |______|_| \_|      |_____/|_|    |______\_____|  |_|  |_|  \_\______|
--                               ______                                                
--                              |______|                                               
-- Module Name: YUV_levels by RD Jordan
-- Created: Early 2023
-- Description: 
-- Dependencies: 
-- Additional Comments: You can view the project here: https://github.com/cfoge/OPEN_SPECTRE-

--NOTE: needs TB, have seen odd behavior in build
library IEEE;
use IEEE.STD_LOGIC_1164.ALL;
use IEEE.STD_LOGIC_ARITH.ALL;
use IEEE.STD_LOGIC_UNSIGNED.ALL;

entity YUV_levels is
    Port ( 
            clk : in std_logic;
            y_signal1 : in STD_LOGIC_VECTOR(11 downto 0) := (others => '0');
           y_signal2 : in STD_LOGIC_VECTOR(11 downto 0);
           y_alpha   : in STD_LOGIC_VECTOR(11 downto 0) := (others => '1');
           y_result  : out STD_LOGIC_VECTOR(11 downto 0);
           u_signal1 : in STD_LOGIC_VECTOR(11 downto 0) := (others => '0');
           u_signal2 : in STD_LOGIC_VECTOR(11 downto 0);
           u_alpha   : in STD_LOGIC_VECTOR(11 downto 0) := (others => '1');
           u_result  : out STD_LOGIC_VECTOR(11 downto 0);
           v_signal1 : in STD_LOGIC_VECTOR(11 downto 0) := (others => '0');
           v_signal2 : in STD_LOGIC_VECTOR(11 downto 0);
           v_alpha   : in STD_LOGIC_VECTOR(11 downto 0) := (others => '1');
           v_result  : out STD_LOGIC_VECTOR(11 downto 0));
end YUV_levels;

architecture Behavioral of YUV_levels is
    component AlphaBlend
        Port ( 
                clk : in std_logic;
                signal1 : in STD_LOGIC_VECTOR(11 downto 0);
               signal2 : in STD_LOGIC_VECTOR(11 downto 0);
               alpha   : in STD_LOGIC_VECTOR(11 downto 0);
               result  : out STD_LOGIC_VECTOR(11 downto 0));
    end component;

    signal y_result_int, u_result_int, v_result_int : integer range 0 to 4095;
begin
    -- Instantiate alpha blend modules
    level_y : AlphaBlend
        port map (
                clk => clk,
                signal1 => y_signal1,
                  signal2 => y_signal2,
                  alpha => y_alpha,
                  result => y_result);

    level_u : AlphaBlend
        port map (
                clk => clk,
                signal1 => u_signal1,
                  signal2 => u_signal2,
                  alpha => u_alpha,
                  result => u_result);

    level_v : AlphaBlend
        port map (
                clk => clk,
                signal1 => v_signal1,
                  signal2 => v_signal2,
                  alpha => v_alpha,
                  result => v_result);
end Behavioral;
