hxlnt/open_spectre/fpga/src/analoge_side/osc/SinWaveGenerator_TB.vhd

--   ____  _____  ______ _   _         _____ _____  ______ _____ _______ _____  ______ 
--  / __ \|  __ \|  ____| \ | |       / ____|  __ \|  ____/ ____|__   __|  __ \|  ____|
-- | |  | | |__) | |__  |  \| |      | (___ | |__) | |__ | |       | |  | |__) | |__   
-- | |  | |  ___/|  __| | . ` |       \___ \|  ___/|  __|| |       | |  |  _  /|  __|  
-- | |__| | |    | |____| |\  |       ____) | |    | |___| |____   | |  | | \ \| |____ 
--  \____/|_|    |______|_| \_|      |_____/|_|    |______\_____|  |_|  |_|  \_\______|
--                               ______                                                
--                              |______|      
-- Create Date: 2023
-- Created by: Rob D Jordan
-- Notes: 


library IEEE;
use IEEE.STD_LOGIC_1164.ALL;
use IEEE.STD_LOGIC_ARITH.ALL;
use IEEE.STD_LOGIC_UNSIGNED.ALL;

entity SinWaveGenerator_TB is
end SinWaveGenerator_TB;

architecture Behavioral of SinWaveGenerator_TB is
    signal clk, reset, sync_in : STD_LOGIC;
    signal sync_sel :  STD_LOGIC_VECTOR(1 downto 0);
    signal sync_plus :  STD_LOGIC := '0';
    signal sync_minus :  STD_LOGIC := '0';
    signal freq :  STD_LOGIC_VECTOR(9 downto 0);
    signal sin_out : STD_LOGIC_VECTOR(11 downto 0);
    signal square_out : STD_LOGIC;
    signal dist_level      : STD_LOGIC_VECTOR(7 downto 0) := (others => '0'); -- distortion wave level
begin
    -- Instantiate the SinWaveGenerator module
    UUT: entity work.SinWaveGenerator
        Port map (
            clk => clk,
            reset => reset,
            freq => freq,
            dist_level => dist_level,
            sync_sel => sync_sel,
            sync_plus => sync_in,
            sync_minus => sync_in,
            sin_out => sin_out,
            square_out => square_out
        );

    -- Clock process
    process
    begin
        clk <= '0';
        wait for 5 ns; -- Adjust this time period based on your clock frequency
        clk <= '1';
        wait for 5 ns; -- Adjust this time period based on your clock frequency
    end process;

    -- Stimulus process
    process
    begin
        reset <= '1';
        freq <= "0000000000";
        sync_in <= '0';
        sync_sel <= "00";
        wait for 10 ns;

        reset <= '0';
        freq <= "0000000101"; -- Set the frequency to your desired value
--        sync_in <= '1';
        wait for 1000 ns; -- Simulate for some time

     
        wait;
    end process;

end Behavioral;
