hxlnt/open_spectre/fpga/src/digital_side/chromanance_outputs/mux_5.vhd

--   ____  _____  ______ _   _         _____ _____  ______ _____ _______ _____  ______ 
--  / __ \|  __ \|  ____| \ | |       / ____|  __ \|  ____/ ____|__   __|  __ \|  ____|
-- | |  | | |__) | |__  |  \| |      | (___ | |__) | |__ | |       | |  | |__) | |__   
-- | |  | |  ___/|  __| | . ` |       \___ \|  ___/|  __|| |       | |  |  _  /|  __|  
-- | |__| | |    | |____| |\  |       ____) | |    | |___| |____   | |  | | \ \| |____ 
--  \____/|_|    |______|_| \_|      |_____/|_|    |______\_____|  |_|  |_|  \_\______|
--                               ______                                                
--                              |______|                                               
-- Module Name: 
-- Created: Early 2023
-- Description: 
-- Dependencies: 
-- Additional Comments: You can view the project here: https://github.com/cfoge/OPEN_SPECTRE-

-- created by   :   RD Jordan
-- 5 paralell 2:1 muxes with a common select

library ieee;
use ieee.std_logic_1164.all;

entity mux_5 is
    port (
        sel: in std_logic;
        a: in std_logic_vector(5 downto 0);
        b: in std_logic_vector(5 downto 0);
        c: out std_logic_vector(5 downto 0)
    );
end mux_5;

architecture behavior of mux_5 is

begin
    mux1: entity work.mux2_1 port map (sel=>sel, a=>a(0), b=>b(0), c=>c(0));
    mux2: entity work.mux2_1 port map (sel=>sel, a=>a(1), b=>b(1), c=>c(1));
    mux3: entity work.mux2_1 port map (sel=>sel, a=>a(2), b=>b(2), c=>c(2));
    mux4: entity work.mux2_1 port map (sel=>sel, a=>a(3), b=>b(3), c=>c(3));
    mux5: entity work.mux2_1 port map (sel=>sel, a=>a(4), b=>b(4), c=>c(4));
    mux6: entity work.mux2_1 port map (sel=>sel, a=>a(5), b=>b(5), c=>c(5));
    
end behavior;
